AlexNecakov/PUCKFish/FlagpoleWeb/android-chrome-192x192.png

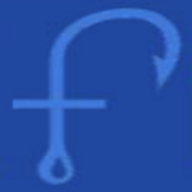
FlagpoleWeb/android-chrome-192x192.png
