AlexNecakov/PUCKFish/Images/1_22 Meeting Notes.jpg

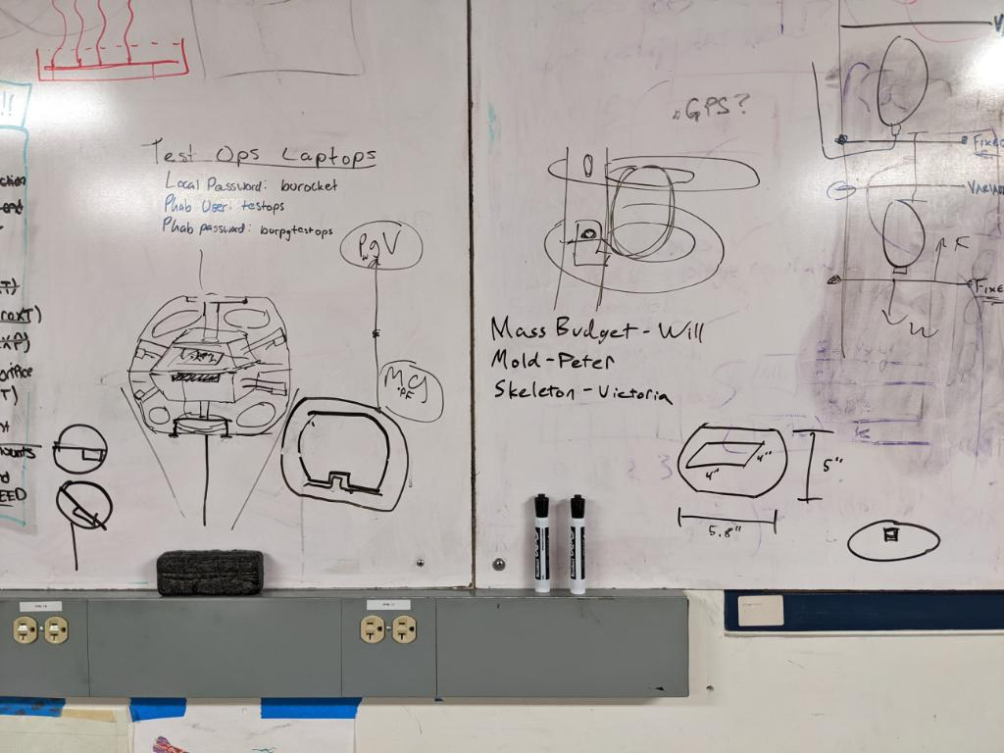
Images/1_22 Meeting Notes.jpg
