AlexNecakov/PUCKFish/Images/color_log.jpg

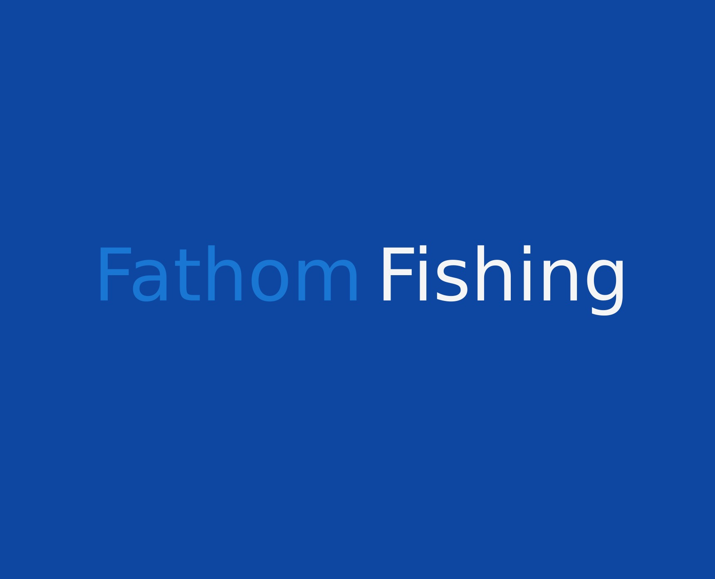
Images/color_log.jpg
