AlexNecakov/PUCKFish/Images/color_log.png

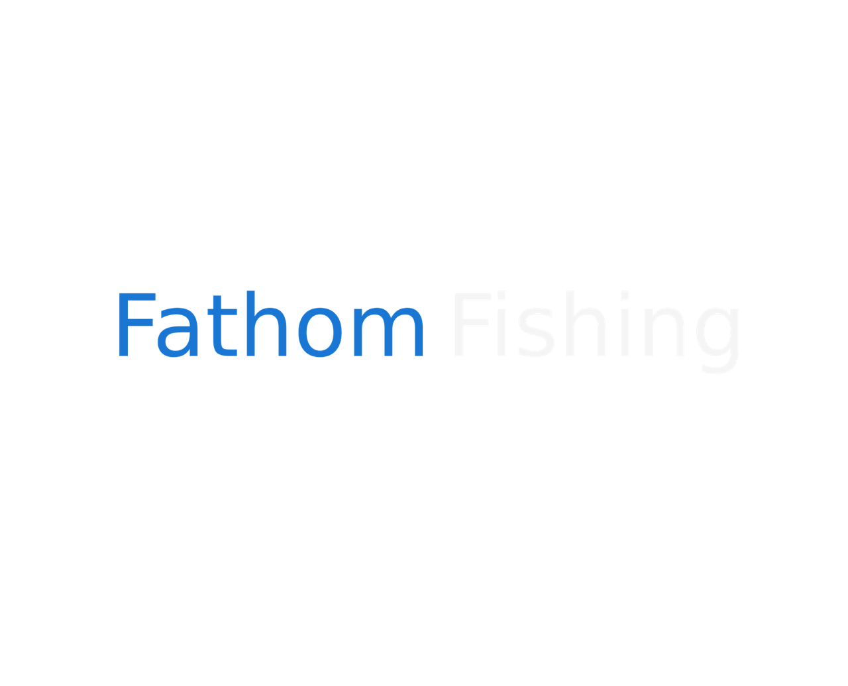
Images/color_log.png
