AlexNecakov/PUCKFish/Images/IMG_20220302_132734_01.jpg

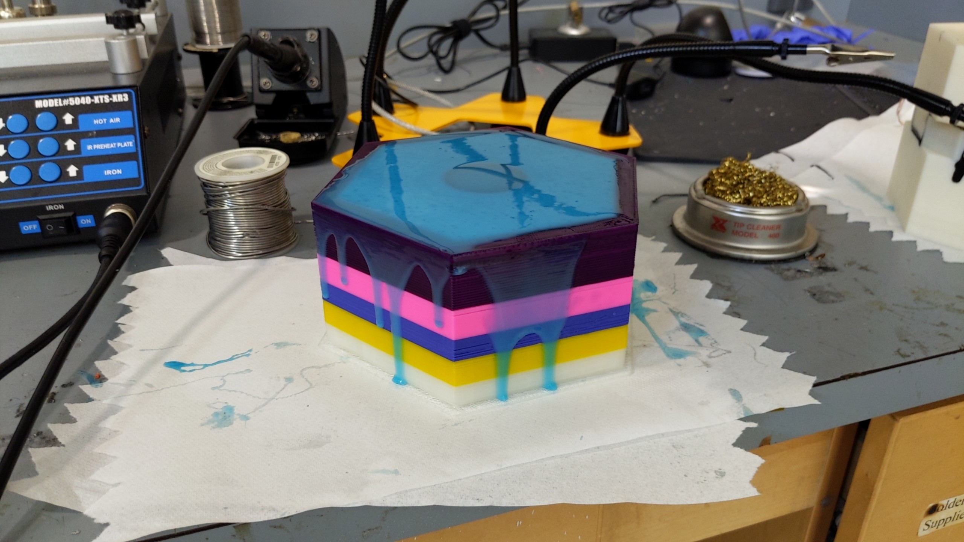
Images/IMG_20220302_132734_01.jpg
