AlexNecakov/PUCKFish/Images/Pill Insert.jpg

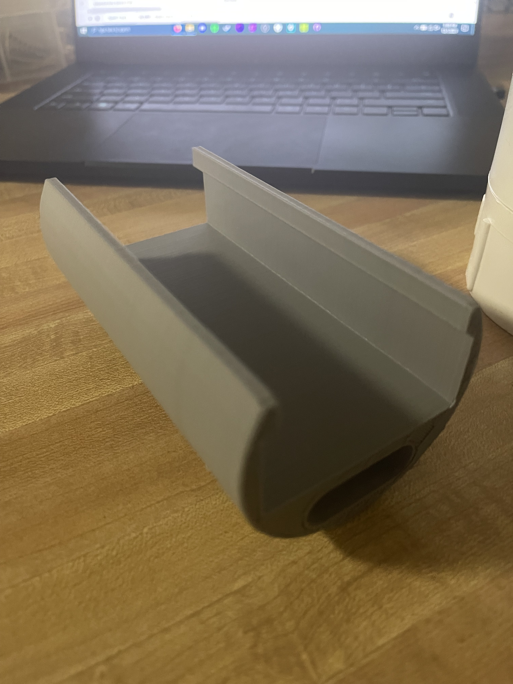
Images/Pill Insert.jpg
