AlexNecakov/PUCKFish/Images/Pill Interior.jpg

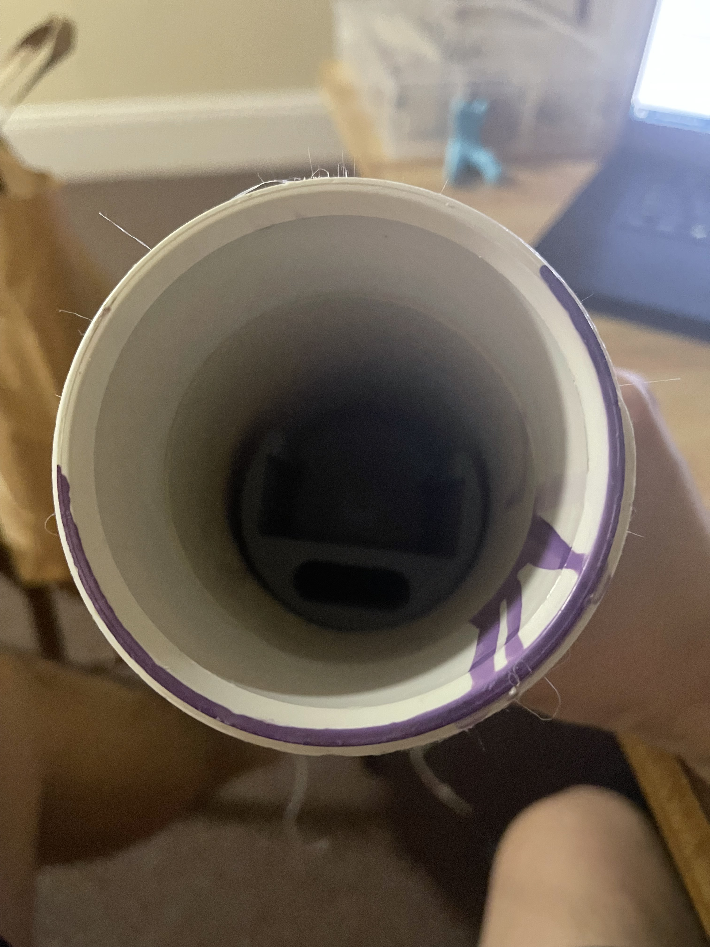
Images/Pill Interior.jpg
