AlexNecakov/PUCKFish/Images/Pill.jpg

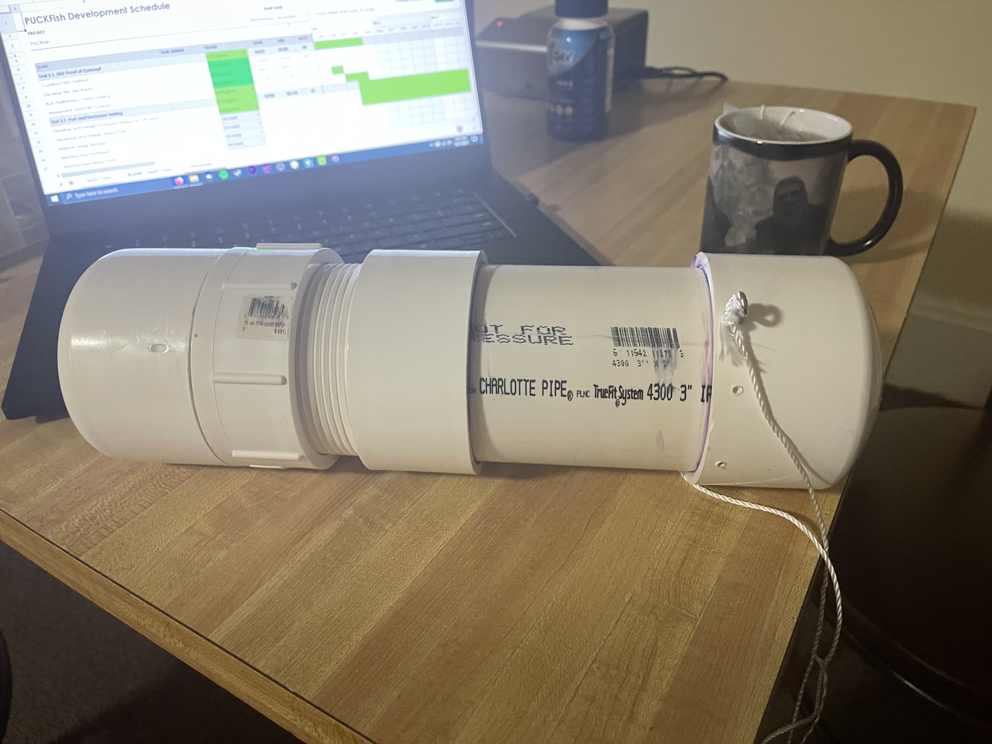
Images/Pill.jpg
