AlexNecakov/PUCKFish/Images/PXL_20211130_193921652.jpg

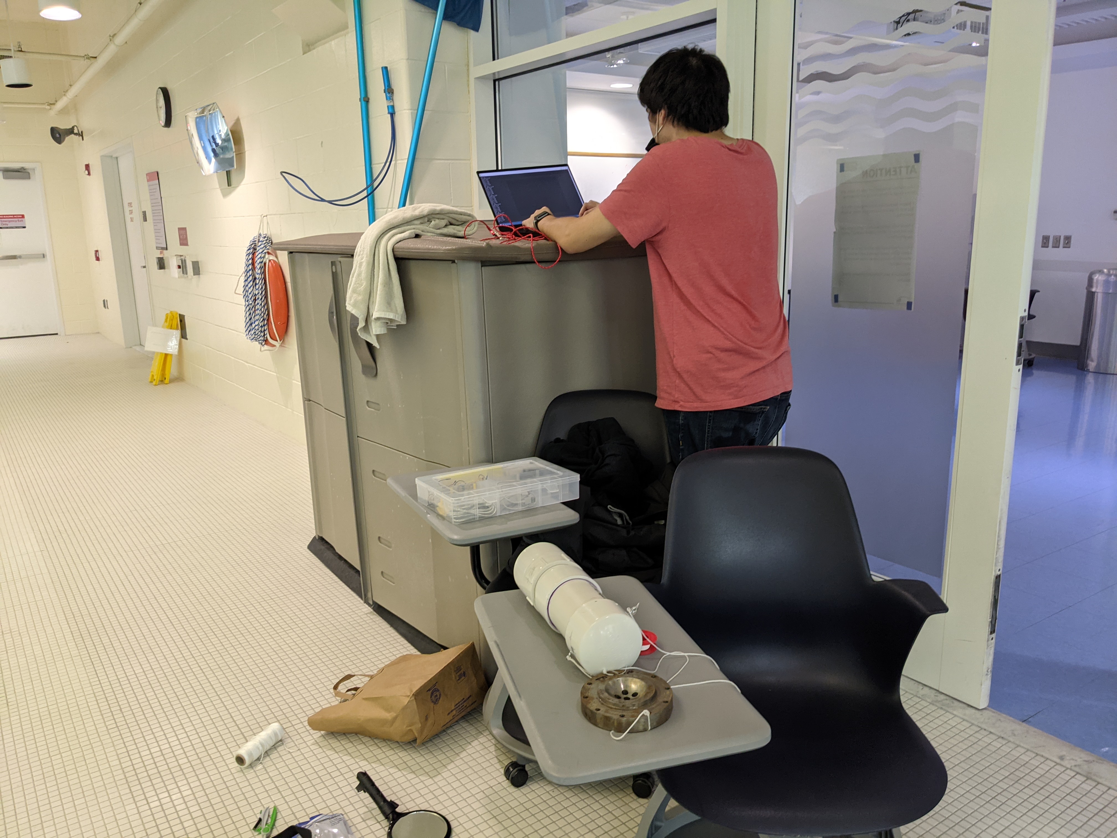
Images/PXL_20211130_193921652.jpg
