AlexNecakov/PUCKFish/Images/PXL_20220228_151510934.jpg

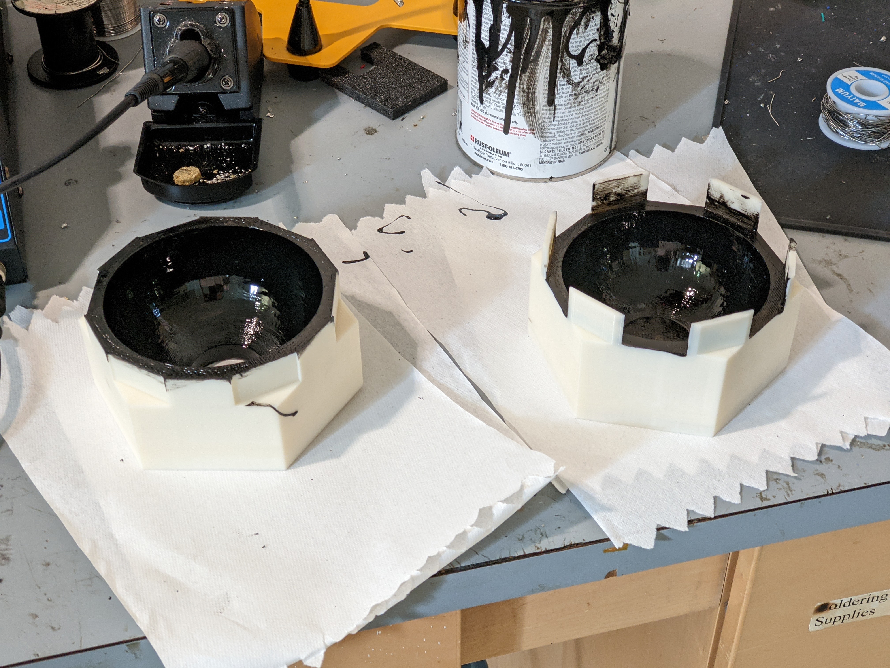
Images/PXL_20220228_151510934.jpg
