AlexNecakov/PUCKFish/Images/PXL_20220301_195429519.jpg

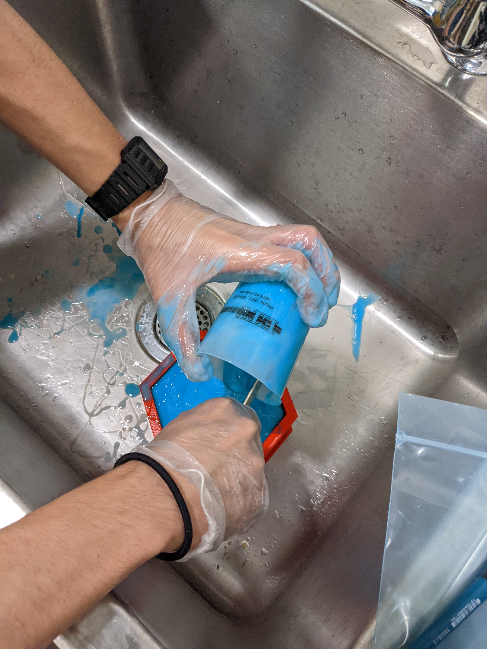
Images/PXL_20220301_195429519.jpg
