AlexNecakov/PUCKFish/Images/PXL_20220301_195727455.jpg

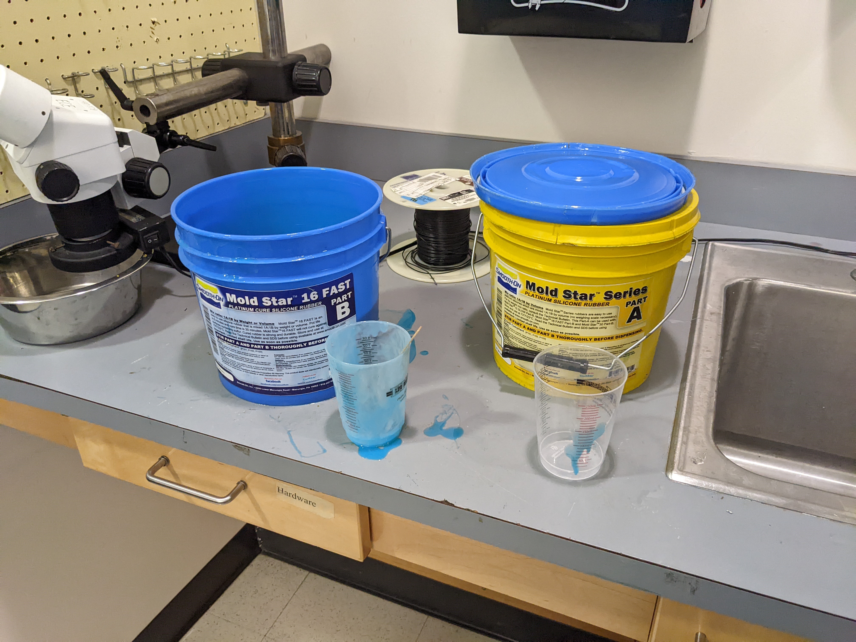
Images/PXL_20220301_195727455.jpg
