AlexNecakov/PUCKFish/Images/PXL_20220301_195731114.jpg

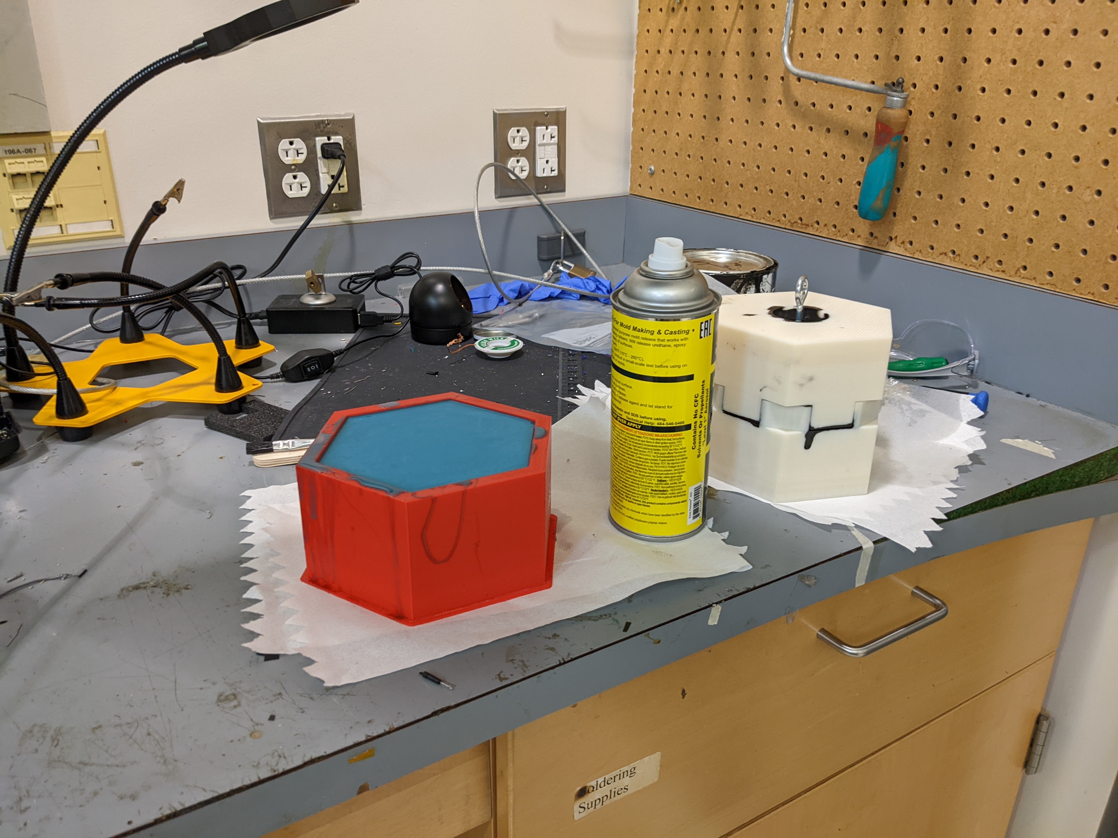
Images/PXL_20220301_195731114.jpg
