AlexNecakov/PUCKFish/Images/PXL_20220302_183742333.jpg

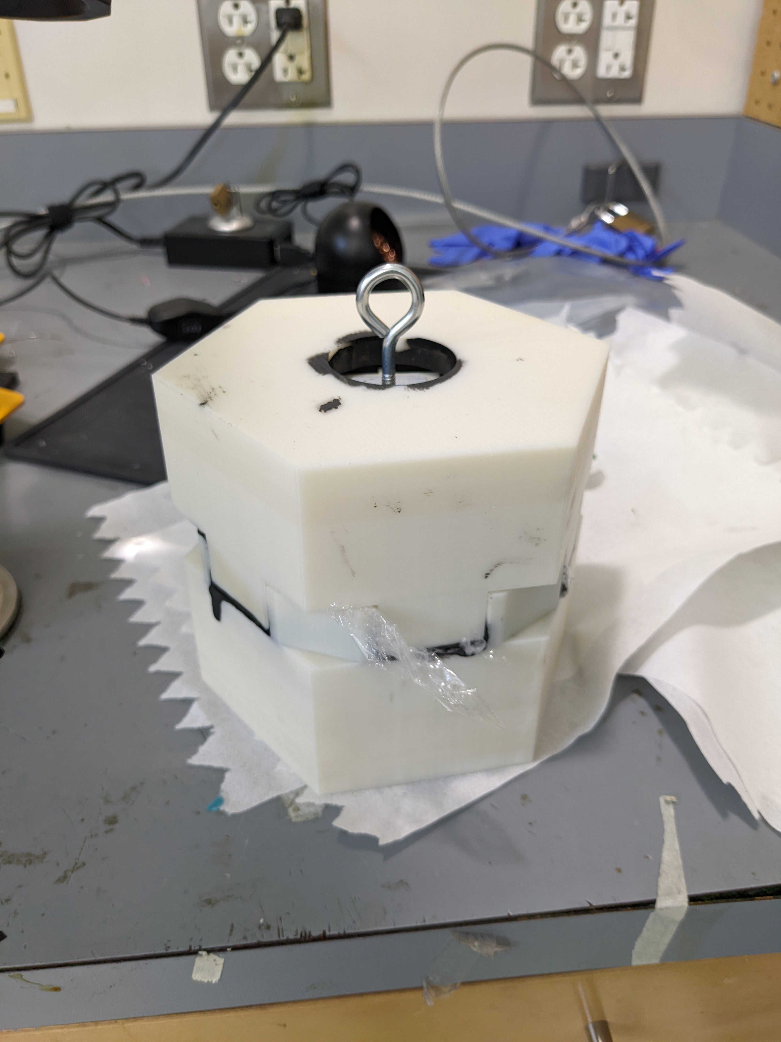
Images/PXL_20220302_183742333.jpg
