AlexNecakov/PUCKFish/PCB/Images/LayoutPCB.PNG

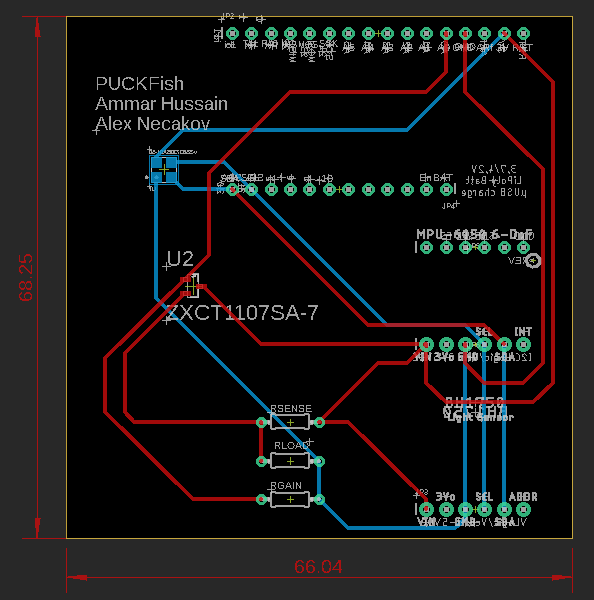
PCB/Images/LayoutPCB.PNG
