AlexNecakov/PUCKFish/PCB/Images/RenderBot.png

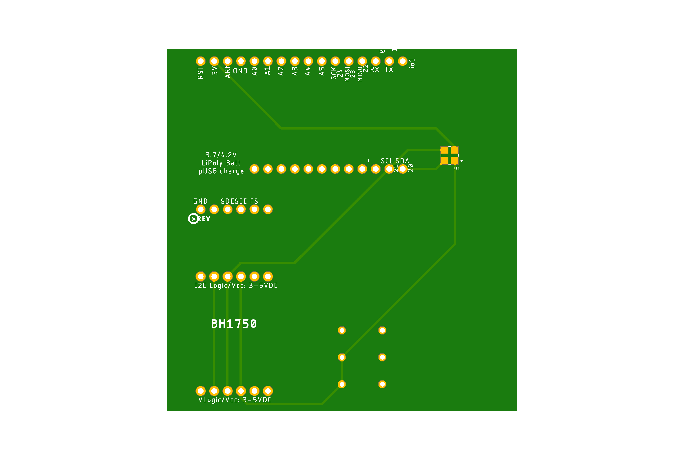
PCB/Images/RenderBot.png
