AlexNecakov/PUCKFish/PCB/Images/RenderTop.png

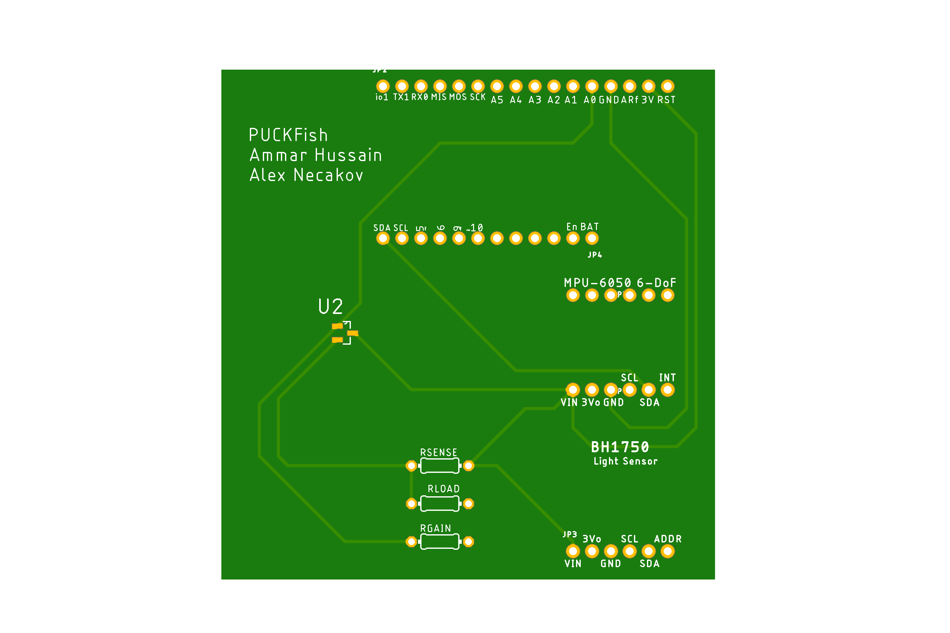
PCB/Images/RenderTop.png
