AlexNecakov/PUCKFish/Poster/PinClipart.com_lobster-clipart_289695.png

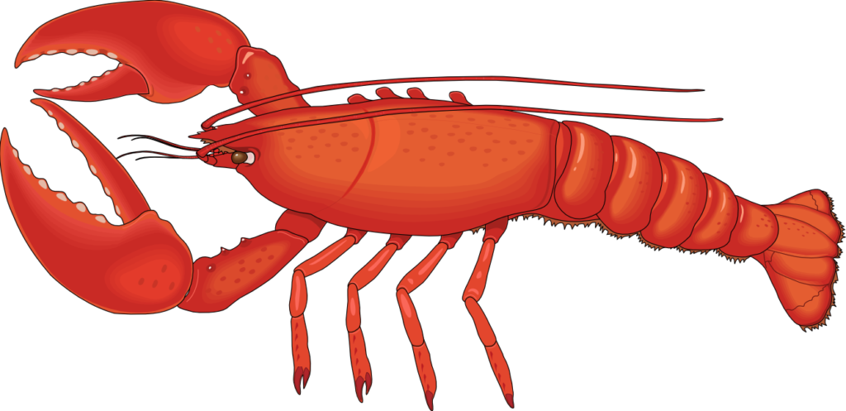
Poster/PinClipart.com_lobster-clipart_289695.png
