AlexNecakov/PUCKFish/Structure CAD/Skeleton/Skeleton_6.SLDPRT

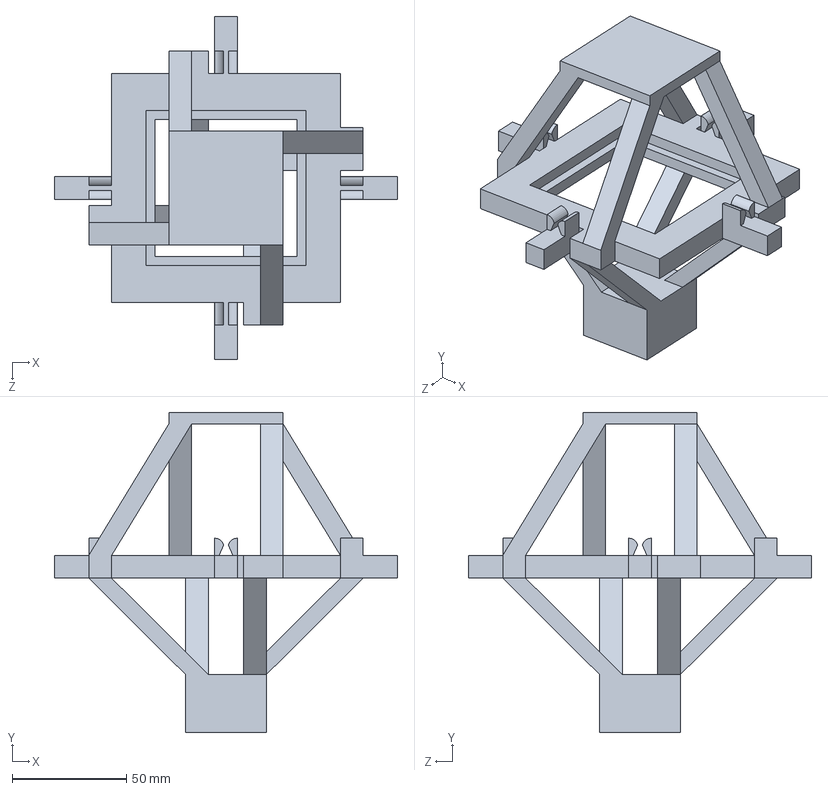
[picture p80: CAD file, 2022-01-28]
Structure CAD/Skeleton/Skeleton_6.SLDPRT
150.0 x 140.0 x 150.0 mm
