AlexNecakov/PUCKFish/Structure CAD/Skeleton/Skeleton_4.SLDPRT

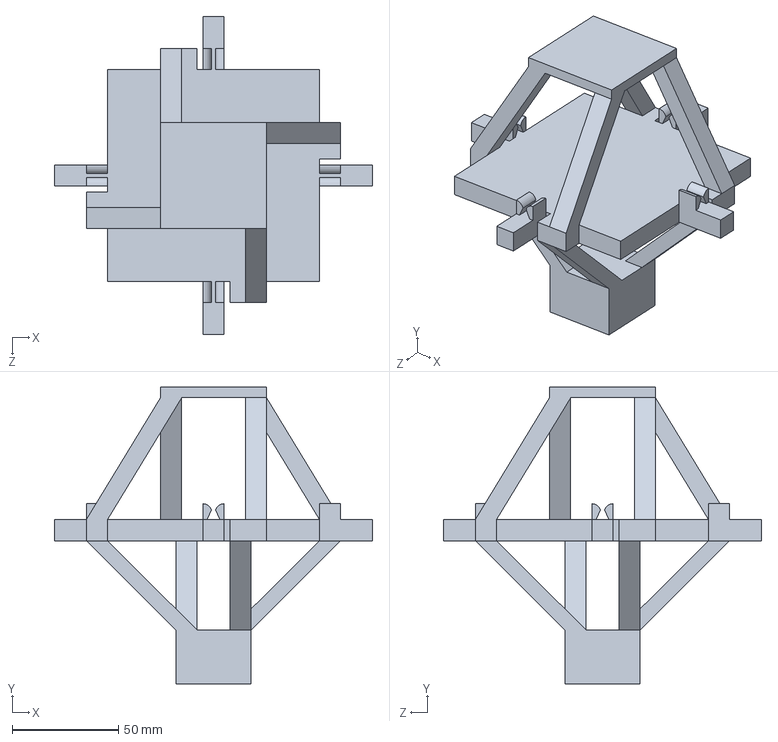
[picture p81: CAD file, 2022-01-25]
Structure CAD/Skeleton/Skeleton_4.SLDPRT
150.0 x 140.0 x 150.0 mm
