AlexNecakov/PUCKFish/Structure CAD/Skeleton/Skeleton_2.SLDPRT

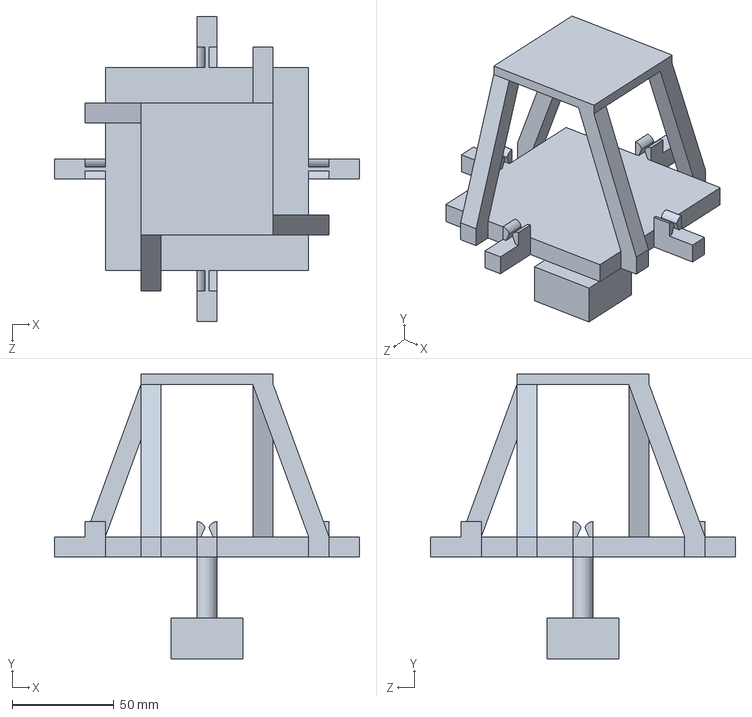
[picture p82: CAD file, 2022-01-25]
Structure CAD/Skeleton/Skeleton_2.SLDPRT
150.0 x 140.0 x 150.0 mm
