AlexNecakov/PUCKFish/Structure CAD/Skeleton/Skeleton_1.SLDPRT

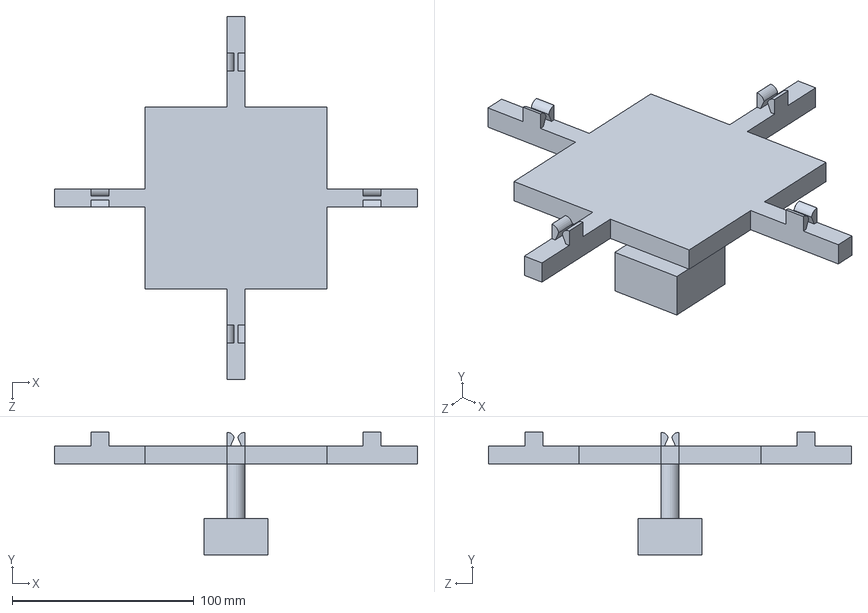
[picture p83: CAD file, 2022-01-25]
Structure CAD/Skeleton/Skeleton_1.SLDPRT
200.0 x 67.5 x 200.0 mm
