AlexNecakov/PUCKFish/Structure CAD/Skeleton/Skeleton_3.SLDPRT

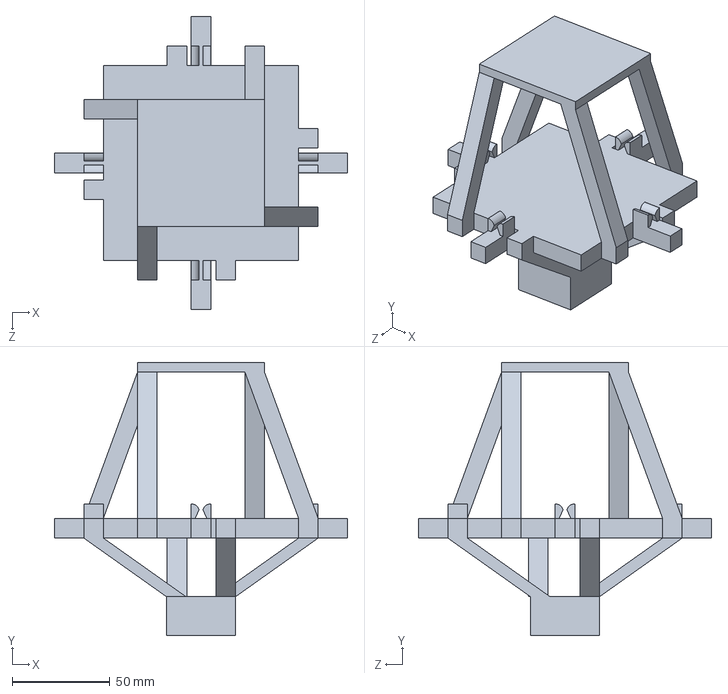
[picture p84: CAD file, 2022-01-25]
Structure CAD/Skeleton/Skeleton_3.SLDPRT
150.0 x 140.0 x 150.0 mm
